EvilForge/FieldFlags/eFlag-ItFits.jpg

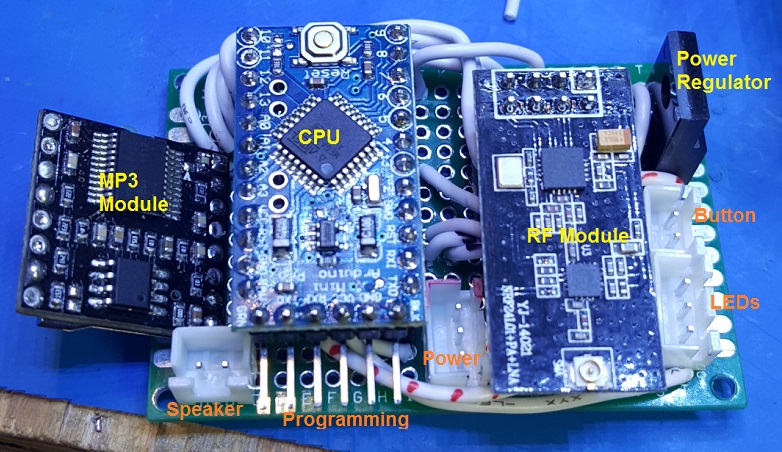
eFlag-ItFits.jpg
