EvilForge/FieldFlags/eFlags-smallbox.jpg

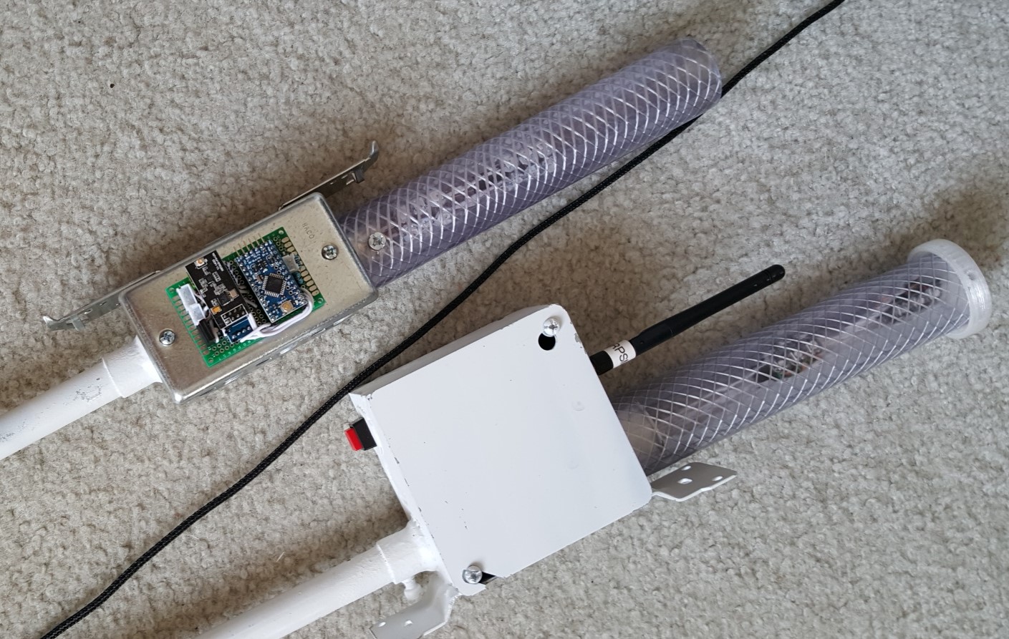
eFlags-smallbox.jpg
