EvilForge/FieldFlags/FlagColor.png

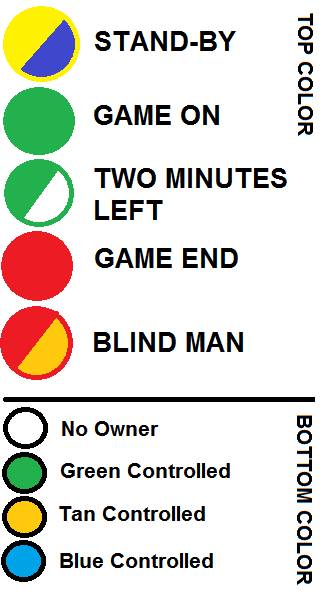
FlagColor.png
