EvilForge/FieldFlags/IMAG0451.jpg

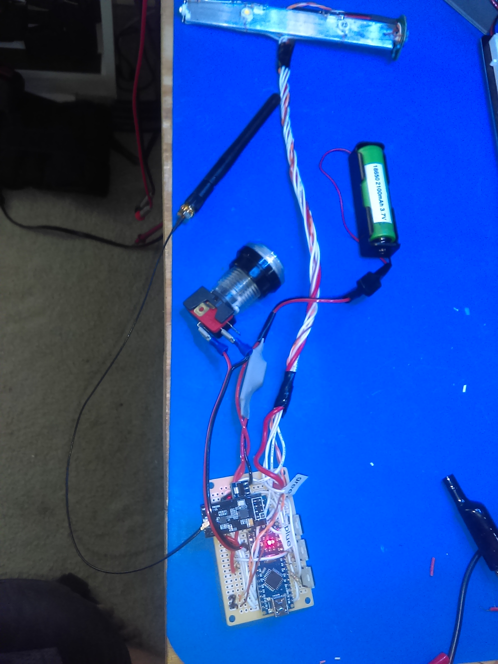
IMAG0451.jpg
