EvilForge/FieldFlags/images/clearmap.png

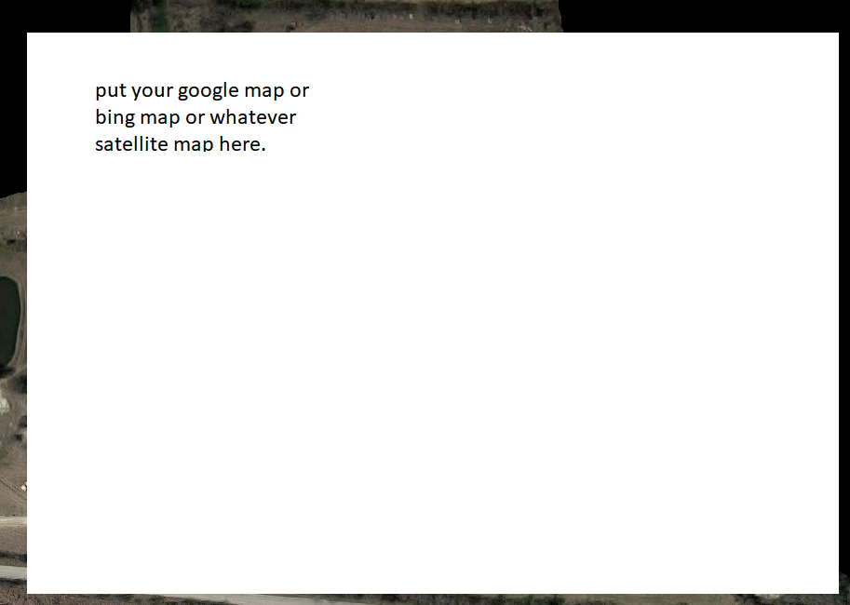
images/clearmap.png
