EvilForge/FieldFlags/images/Flag Progress.png

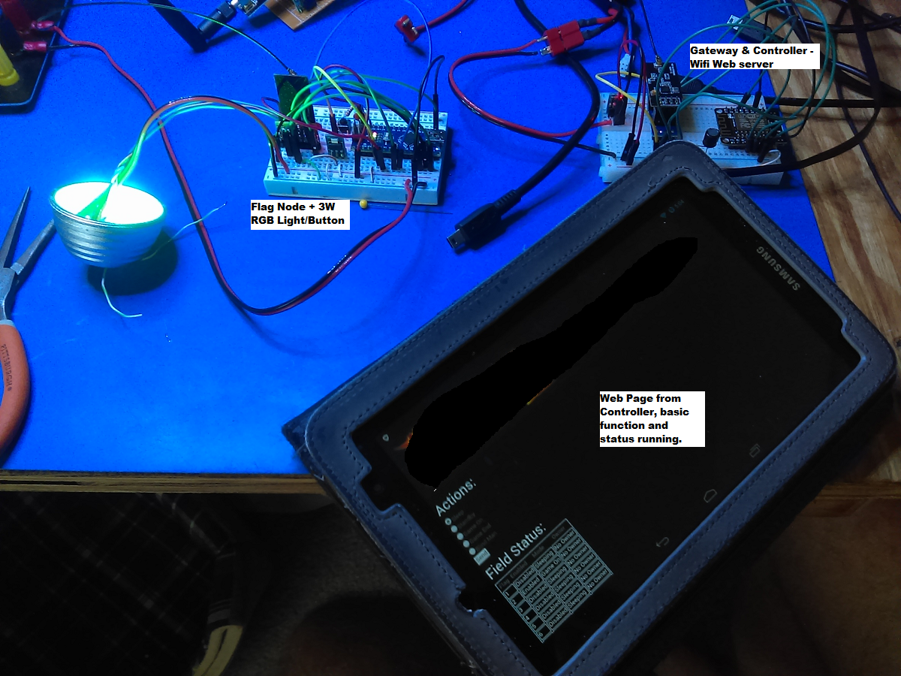
images/Flag Progress.png
