EvilForge/FieldFlags/NRF24L01 PA LNA.jpg

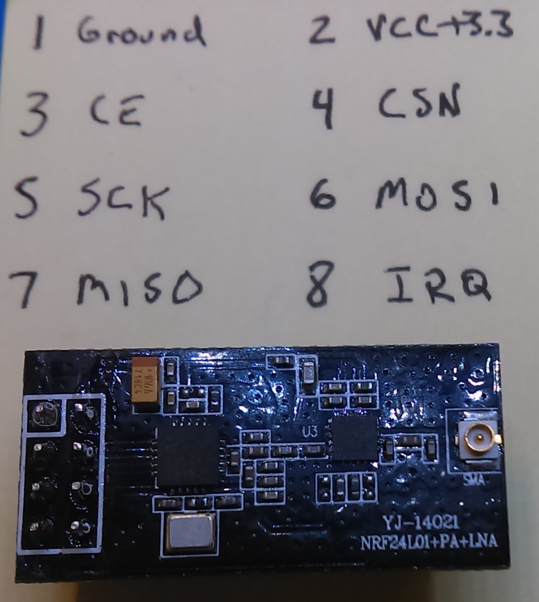
NRF24L01 PA LNA.jpg
